wannabecoffeenerd/hillside/hillsideview46/doc/image/hotswap_switch_on_pcb.jpg

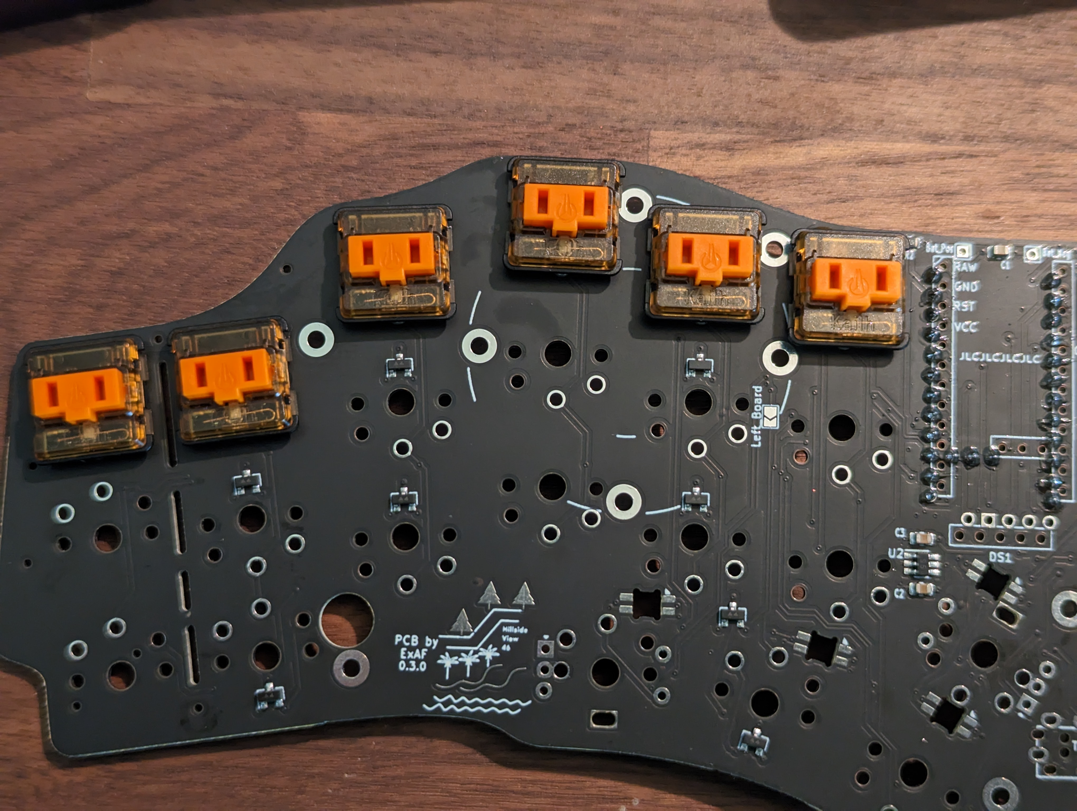
hillsideview46/doc/image/hotswap_switch_on_pcb.jpg
