wannabecoffeenerd/hillside/hillsideview46/doc/image/hsv_3x5_chicago_steno.jpg

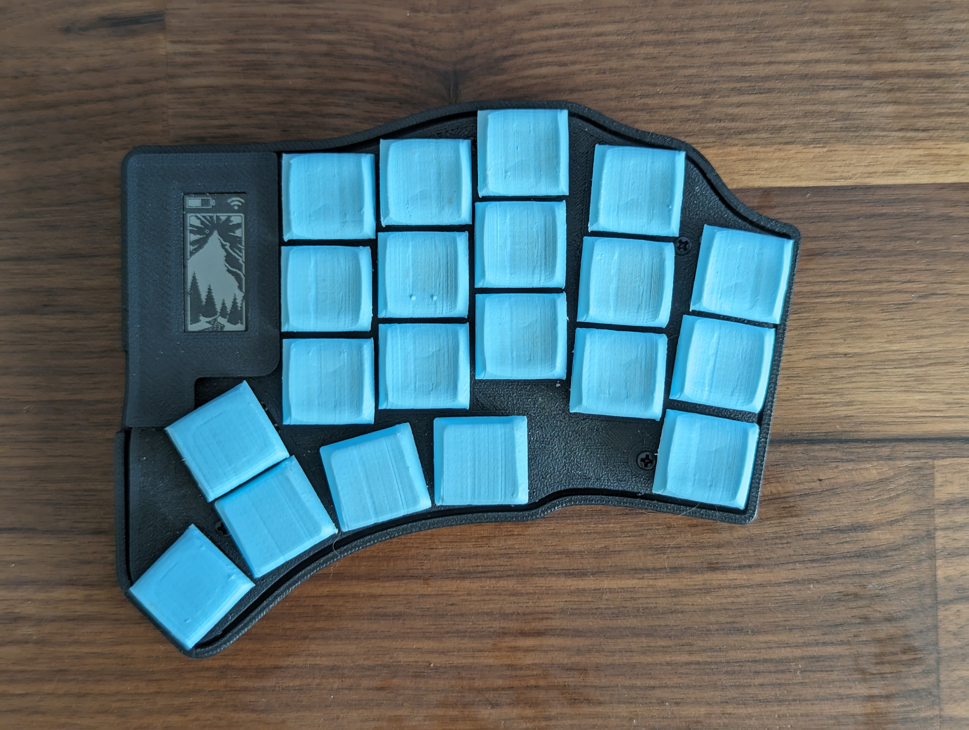
hillsideview46/doc/image/hsv_3x5_chicago_steno.jpg
