wannabecoffeenerd/hillside/hillsideview46/doc/image/hsv_breakoff.jpg

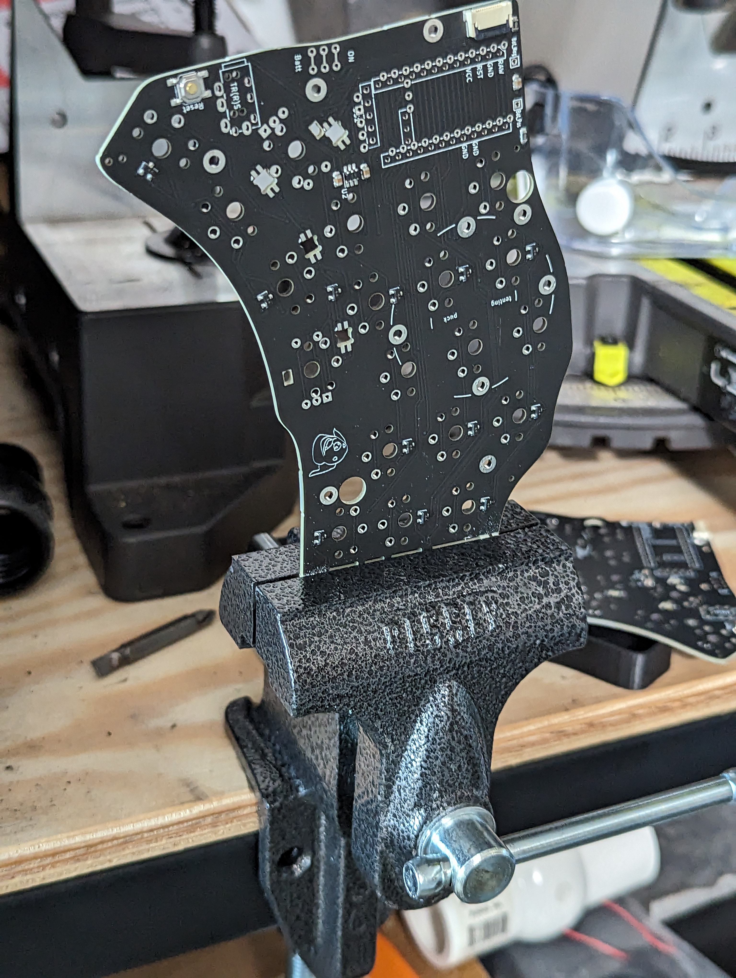
hillsideview46/doc/image/hsv_breakoff.jpg
