wannabecoffeenerd/hillside/hillsideview46/doc/image/hsv_tenting.jpg

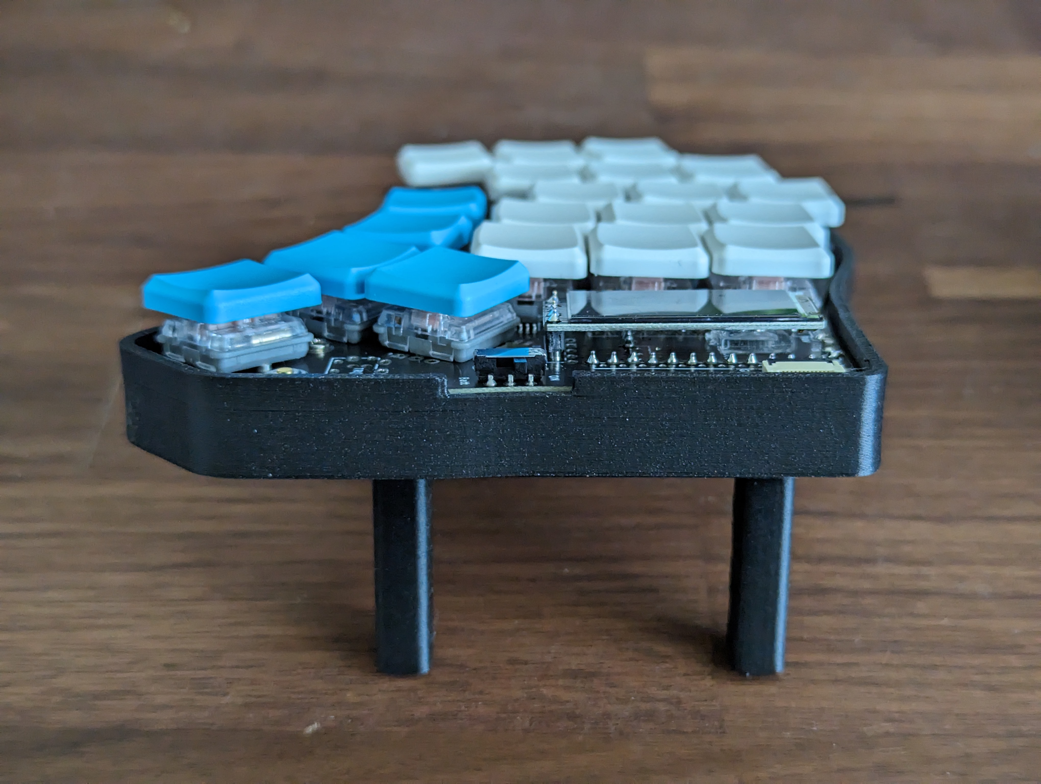
hillsideview46/doc/image/hsv_tenting.jpg
