wannabecoffeenerd/hillside/hillsideview46/doc/image/hsv_usbc.jpg

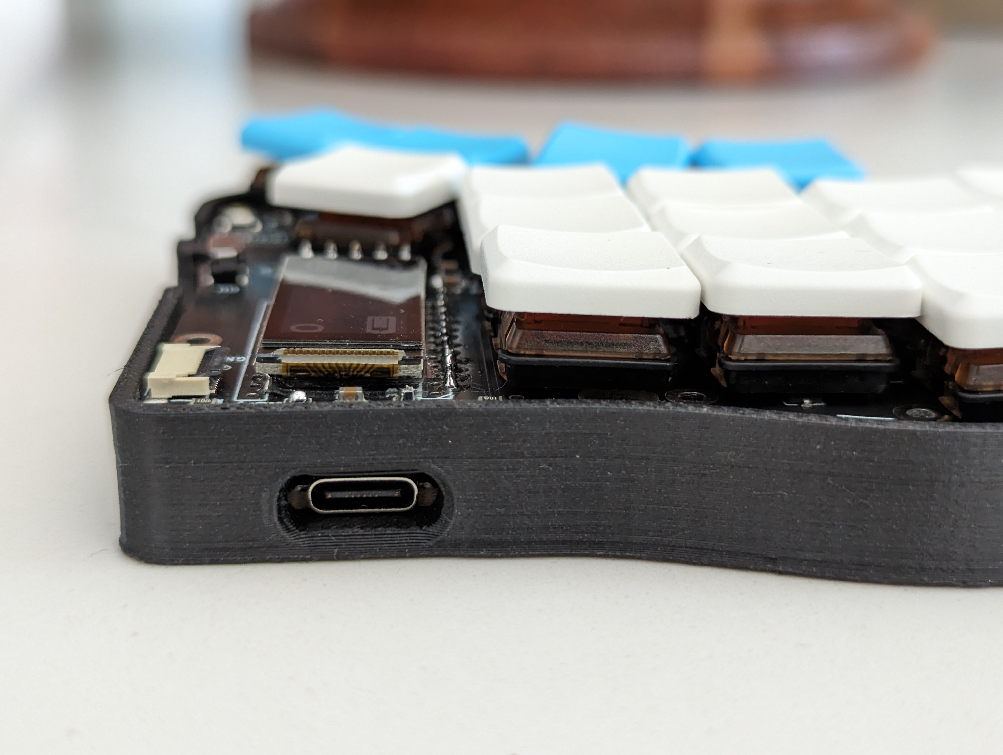
hillsideview46/doc/image/hsv_usbc.jpg
