wannabecoffeenerd/hillside/hillsideview46/doc/image/nice_nano_millmax_prep.jpg

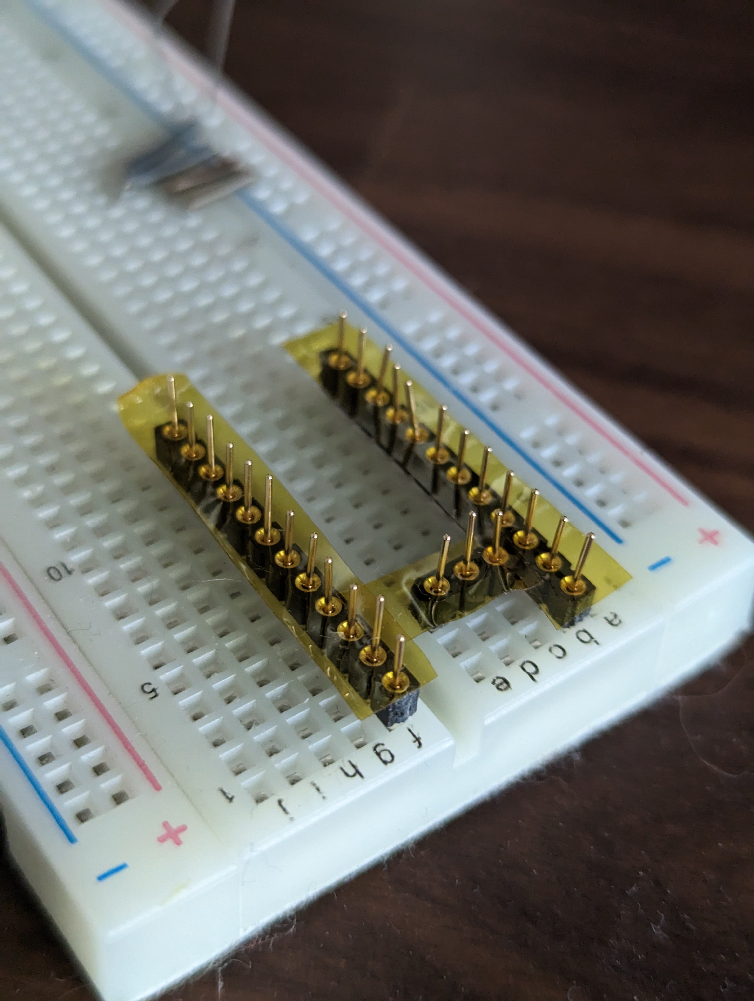
hillsideview46/doc/image/nice_nano_millmax_prep.jpg
