wannabecoffeenerd/hillside/hillsideview46/doc/image/nice_view_support_tape.jpg

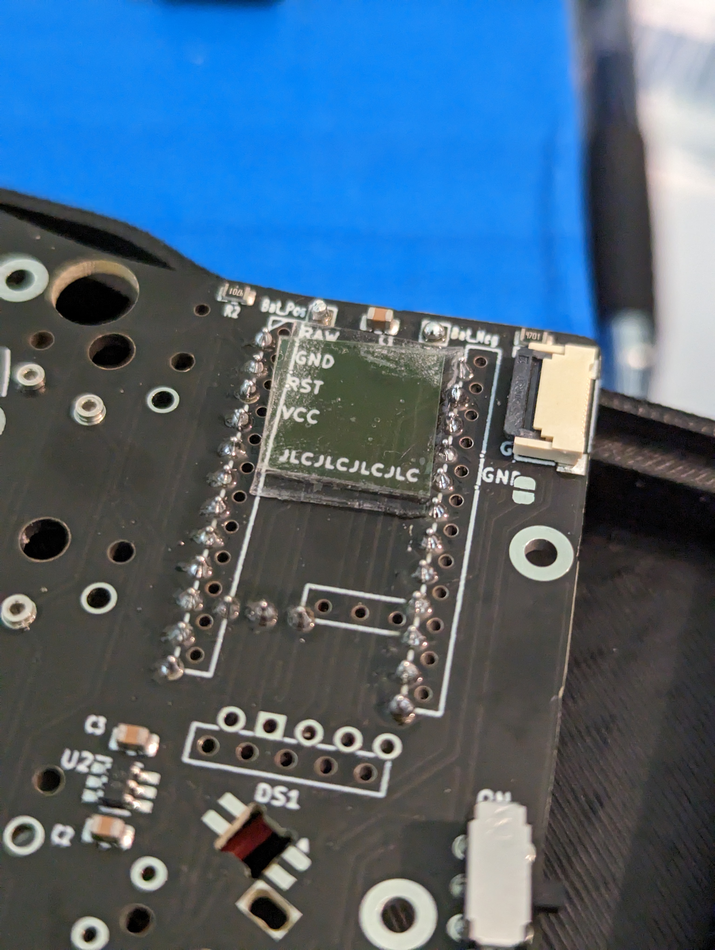
hillsideview46/doc/image/nice_view_support_tape.jpg
