wannabecoffeenerd/hillside/hillsideview46/doc/image/battery_soldering.jpg

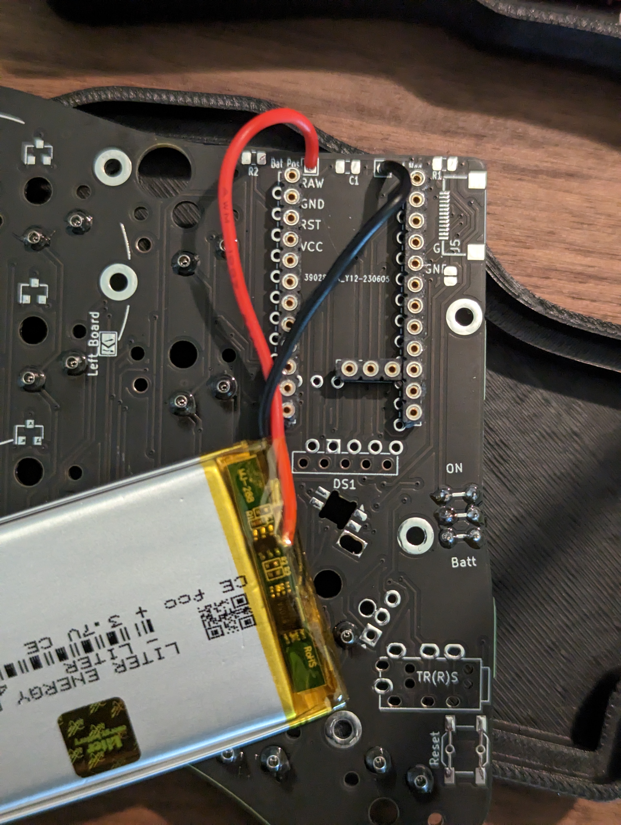
hillsideview46/doc/image/battery_soldering.jpg
