wannabecoffeenerd/hillside/hillsideview46/doc/image/hotswap_soldering.jpg

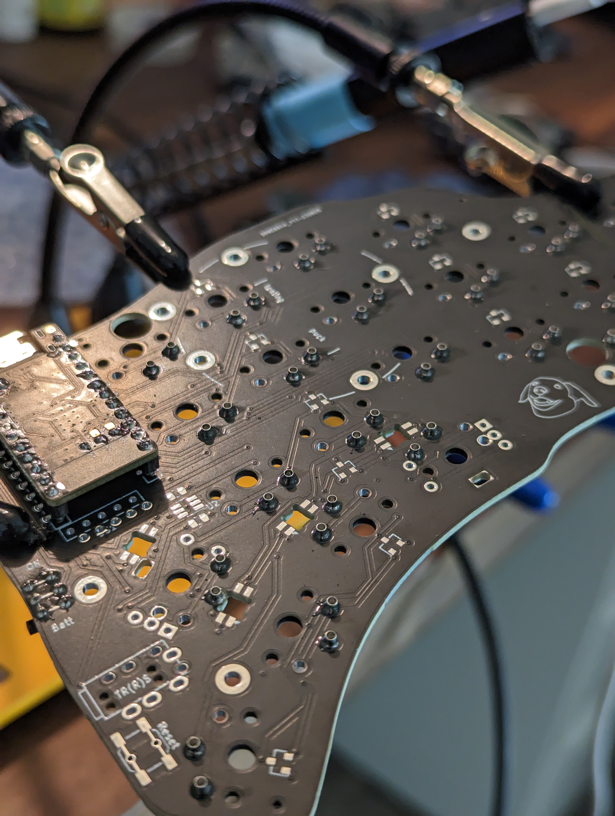
hillsideview46/doc/image/hotswap_soldering.jpg
