wannabecoffeenerd/hillside/hillsideview46/doc/image/millmax_soldering.jpg

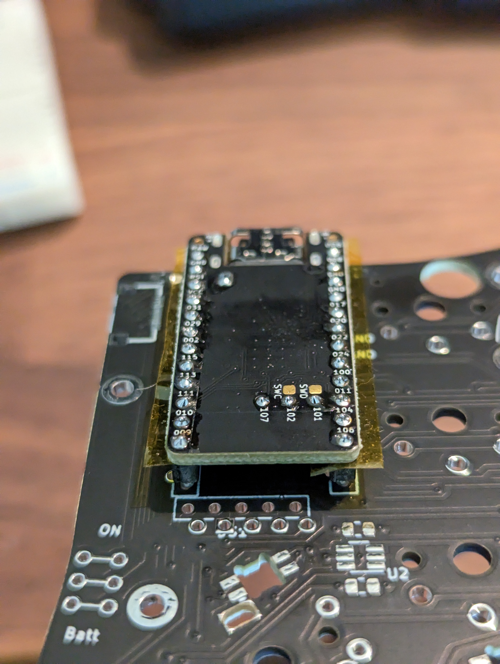
hillsideview46/doc/image/millmax_soldering.jpg
