wannabecoffeenerd/hillside/hillsideview46/doc/image/nice_nano_soldering.jpg

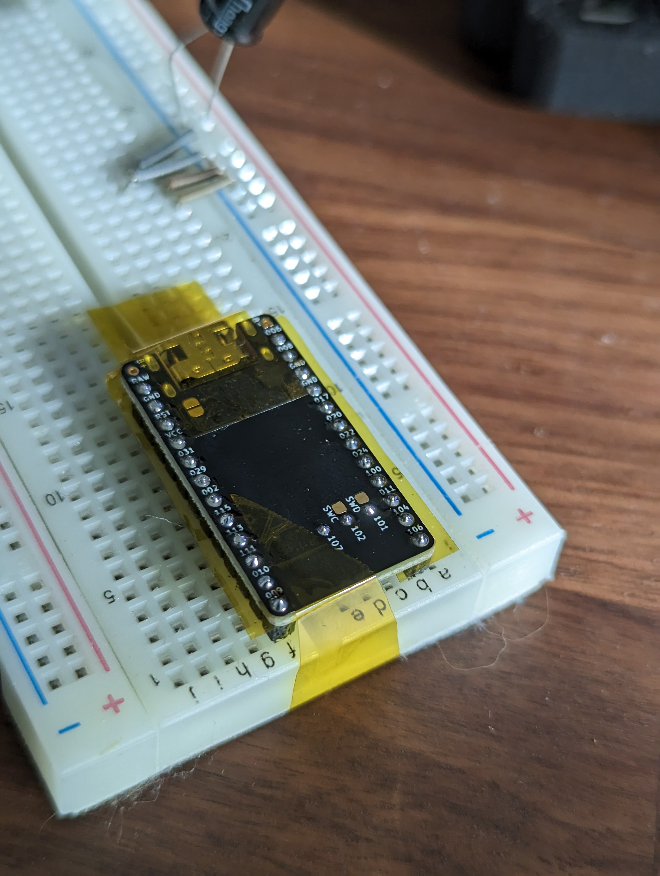
hillsideview46/doc/image/nice_nano_soldering.jpg
